SteveW25561/Tomy-Enterprise-Refit-Homekit-ESP32/enterprise_homekit/phaser_mp3.h

// Phaser sound — mono 221kbps MP3, ~689ms
const uint8_t PHASER_MP3[] PROGMEM = {
  0xFF, 0xFB, 0xB8, 0xC4, 0x00, 0x00, 0x00, 0x00, 0x00, 0x00, 0x00, 0x00, 0x00, 0x00, 0x00, 0x00,
  0x00, 0x00, 0x00, 0x00, 0x00, 0x49, 0x6E, 0x66, 0x6F, 0x00, 0x00, 0x00, 0x0F, 0x00, 0x00, 0x00,
  0x15, 0x00, 0x00, 0x4A, 0x40, 0x00, 0x0C, 0x0C, 0x0C, 0x0C, 0x18, 0x18, 0x18, 0x18, 0x18, 0x24,
  0x24, 0x24, 0x24, 0x24, 0x30, 0x30, 0x30, 0x30, 0x30, 0x3C, 0x3C, 0x3C, 0x3C, 0x49, 0x49, 0x49,
  0x49, 0x49, 0x55, 0x55, 0x55, 0x55, 0x55, 0x61, 0x61, 0x61, 0x61, 0x61, 0x6D, 0x6D, 0x6D, 0x6D,
  0x79, 0x79, 0x79, 0x79, 0x79, 0x86, 0x86, 0x86, 0x86, 0x86, 0x92, 0x92, 0x92, 0x92, 0x92, 0x9E,
  0x9E, 0x9E, 0x9E, 0xAA, 0xAA, 0xAA, 0xAA, 0xAA, 0xB6, 0xB6, 0xB6, 0xB6, 0xB6, 0xC3, 0xC3, 0xC3,
  0xC3, 0xC3, 0xCF, 0xCF, 0xCF, 0xCF, 0xDB, 0xDB, 0xDB, 0xDB, 0xDB, 0xE7, 0xE7, 0xE7, 0xE7, 0xE7,
  0xF3, 0xF3, 0xF3, 0xF3, 0xF3, 0xFF, 0xFF, 0xFF, 0xFF, 0x00, 0x00, 0x00, 0x39, 0x4C, 0x41, 0x4D,
  0x45, 0x33, 0x2E, 0x31, 0x30, 0x30, 0x01, 0xA0, 0x00, 0x00, 0x00, 0x00, 0x00, 0x00, 0x00, 0x00,
  0x14, 0xC0, 0x24, 0x06, 0x1C, 0x21, 0x00, 0x00, 0xC0, 0x00, 0x00, 0x4A, 0x40, 0xDD, 0x70, 0x2B,
  0x68, 0x00, 0x00, 0x00, 0x00, 0x00, 0x00, 0x00, 0x00, 0x00, 0x00, 0x00, 0x00, 0x00, 0x00, 0x00,
  0x00, 0x00, 0x00, 0x00, 0x00, 0x00, 0x00, 0x00, 0x00, 0x00, 0x00, 0x00, 0x00, 0x00, 0x00, 0x00,
  0x00, 0x00, 0x00, 0x00, 0x00, 0x00, 0x00, 0x00, 0x00, 0x00, 0x00, 0x00, 0x00, 0x00, 0x00, 0x00,
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
  0x00, 0x00, 0x00, 0x00, 0x00, 0x00, 0x00, 0x00, 0x00, 0x00, 0x00, 0x00, 0x00, 0x00, 0x00, 0x00,
  0x00, 0x00, 0x00, 0x00, 0x00, 0x00, 0x00, 0x00, 0x00, 0x00, 0x00, 0x00, 0x00, 0x00, 0x00, 0x00,
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
};
const size_t PHASER_MP3_LEN = 19008;
