SteveW25561/Tomy-Enterprise-Refit-Homekit-ESP32/enterprise_homekit/torpedo_mp3.h

// Torpedo sound — mono 219kbps MP3, ~759ms
const uint8_t TORPEDO_MP3[] PROGMEM = {
  0xFF, 0xFB, 0xB8, 0xC4, 0x00, 0x00, 0x00, 0x00, 0x00, 0x00, 0x00, 0x00, 0x00, 0x00, 0x00, 0x00,
  0x00, 0x00, 0x00, 0x00, 0x00, 0x49, 0x6E, 0x66, 0x6F, 0x00, 0x00, 0x00, 0x0F, 0x00, 0x00, 0x00,
  0x17, 0x00, 0x00, 0x51, 0x00, 0x00, 0x0B, 0x0B, 0x0B, 0x0B, 0x16, 0x16, 0x16, 0x16, 0x21, 0x21,
  0x21, 0x21, 0x21, 0x2C, 0x2C, 0x2C, 0x2C, 0x37, 0x37, 0x37, 0x37, 0x42, 0x42, 0x42, 0x42, 0x42,
  0x4D, 0x4D, 0x4D, 0x4D, 0x59, 0x59, 0x59, 0x59, 0x64, 0x64, 0x64, 0x64, 0x64, 0x6F, 0x6F, 0x6F,
  0x6F, 0x7A, 0x7A, 0x7A, 0x7A, 0x85, 0x85, 0x85, 0x85, 0x85, 0x90, 0x90, 0x90, 0x90, 0x9B, 0x9B,
  0x9B, 0x9B, 0xA6, 0xA6, 0xA6, 0xA6, 0xA6, 0xB2, 0xB2, 0xB2, 0xB2, 0xBD, 0xBD, 0xBD, 0xBD, 0xC8,
  0xC8, 0xC8, 0xC8, 0xC8, 0xD3, 0xD3, 0xD3, 0xD3, 0xDE, 0xDE, 0xDE, 0xDE, 0xE9, 0xE9, 0xE9, 0xE9,
  0xE9, 0xF4, 0xF4, 0xF4, 0xF4, 0xFF, 0xFF, 0xFF, 0xFF, 0x00, 0x00, 0x00, 0x39, 0x4C, 0x41, 0x4D,
  0x45, 0x33, 0x2E, 0x31, 0x30, 0x30, 0x01, 0xA0, 0x00, 0x00, 0x00, 0x00, 0x00, 0x00, 0x00, 0x00,
  0x14, 0xC0, 0x24, 0x06, 0x54, 0x21, 0x00, 0x00, 0xC0, 0x00, 0x00, 0x51, 0x00, 0x7C, 0x64, 0x56,
  0xB6, 0x00, 0x00, 0x00, 0x00, 0x00, 0x00, 0x00, 0x00, 0x00, 0x00, 0x00, 0x00, 0x00, 0x00, 0x00,
  0x00, 0x00, 0x00, 0x00, 0x00, 0x00, 0x00, 0x00, 0x00, 0x00, 0x00, 0x00, 0x00, 0x00, 0x00, 0x00,
  0x00, 0x00, 0x00, 0x00, 0x00, 0x00, 0x00, 0x00, 0x00, 0x00, 0x00, 0x00, 0x00, 0x00, 0x00, 0x00,
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
  0x00, 0x00, 0x00, 0x00, 0x00, 0x00, 0x00, 0x00, 0x00, 0x00, 0x00, 0x00, 0x00, 0x00, 0x00, 0x00,
  0x00, 0x00, 0x00, 0x00, 0x00, 0x00, 0x00, 0x00, 0x00, 0x00, 0x00, 0x00, 0x00, 0x00, 0x00, 0x00,
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
};
const size_t TORPEDO_MP3_LEN = 20736;
